phfbertoleti/ProjetoQCON2016/Interface Web (com criptografia)/consumo.jpg

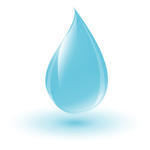
Interface Web (com criptografia)/consumo.jpg
