phfbertoleti/ProjetoQCON2016/Interface Web (com criptografia)/luminosidade.png

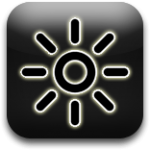
Interface Web (com criptografia)/luminosidade.png
