phfbertoleti/ProjetoQCON2016/Interface Web (com criptografia)/meta.png

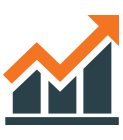
Interface Web (com criptografia)/meta.png
