phfbertoleti/ProjetoQCON2016/Interface Web (com criptografia)/ok.png

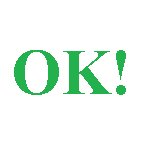
Interface Web (com criptografia)/ok.png
