phfbertoleti/ProjetoQCON2016/Interface Web (com criptografia)/temperatura.jpg

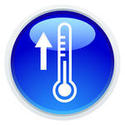
Interface Web (com criptografia)/temperatura.jpg
