phfbertoleti/ProjetoQCON2016/Interface Web (com criptografia)/vazao.png

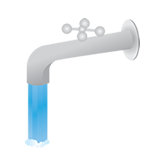
Interface Web (com criptografia)/vazao.png
